ItsAlphie/The-RGB-of-Haptics/HPCT_Unity/Assets/Materials/GOLDDark.png

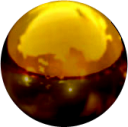
HPCT_Unity/Assets/Materials/GOLDDark.png
