ItsAlphie/The-RGB-of-Haptics/HPCT_Unity/Assets/Downloaded/jewelry_shop/textures/T_.png

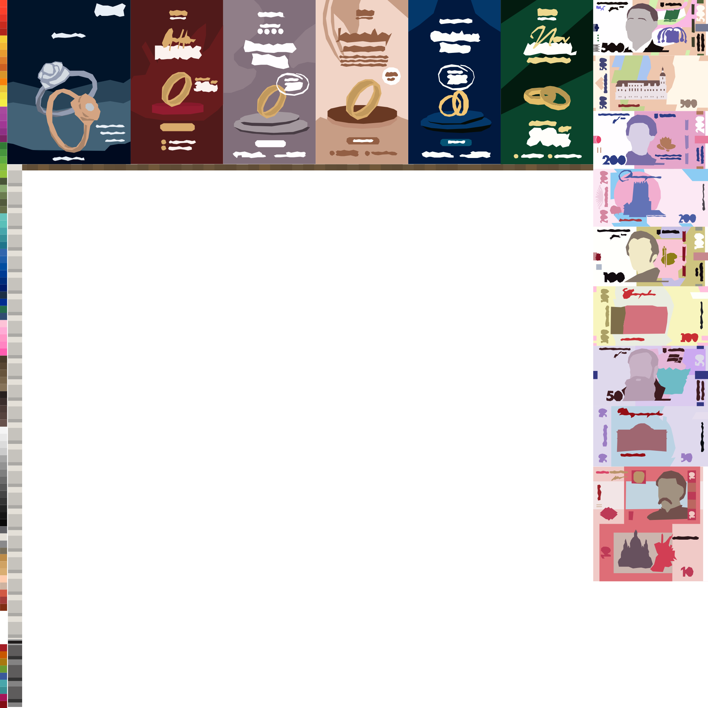
HPCT_Unity/Assets/Downloaded/jewelry_shop/textures/T_.png
