ItsAlphie/The-RGB-of-Haptics/HPCT_Unity/Assets/Mugs, Bowls and Plates/Textures/bowl01_ao.png

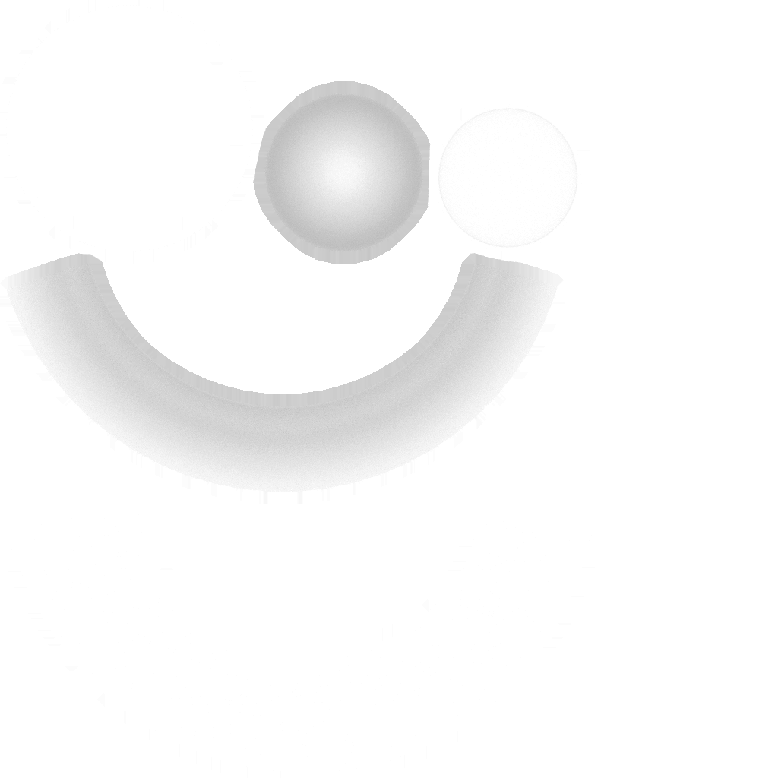
HPCT_Unity/Assets/Mugs, Bowls and Plates/Textures/bowl01_ao.png
