ItsAlphie/The-RGB-of-Haptics/HPCT_Unity/Assets/Mugs, Bowls and Plates/Textures/bowl03.png

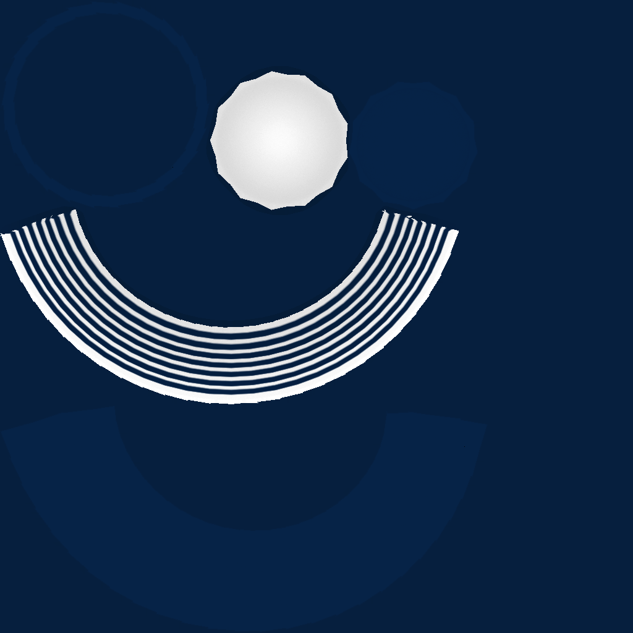
HPCT_Unity/Assets/Mugs, Bowls and Plates/Textures/bowl03.png
