ItsAlphie/The-RGB-of-Haptics/HPCT_Unity/Assets/Mugs, Bowls and Plates/Textures/mug01_rgh.png

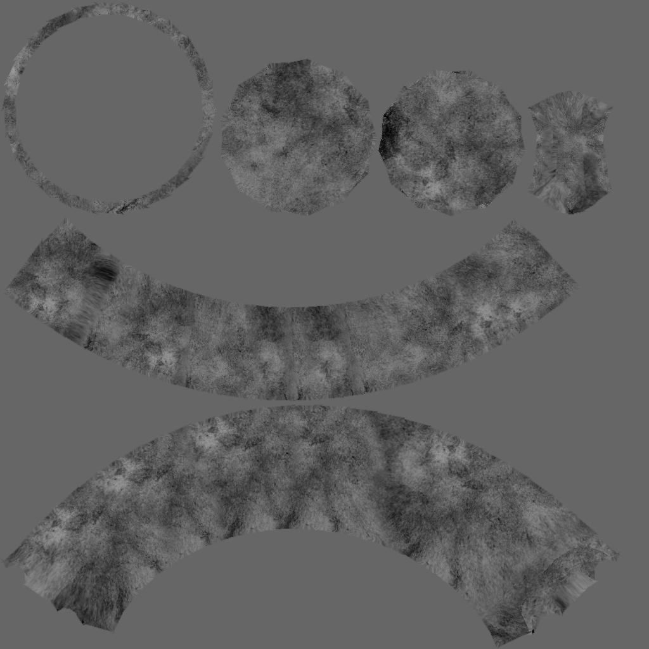
HPCT_Unity/Assets/Mugs, Bowls and Plates/Textures/mug01_rgh.png
