ItsAlphie/The-RGB-of-Haptics/HPCT_Unity/Assets/Mugs, Bowls and Plates/Textures/mug02_ao.png

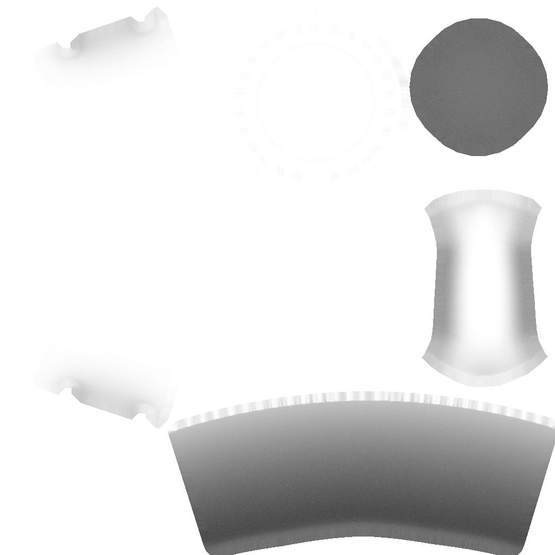
HPCT_Unity/Assets/Mugs, Bowls and Plates/Textures/mug02_ao.png
