ItsAlphie/The-RGB-of-Haptics/HPCT_Unity/Assets/Mugs, Bowls and Plates/Textures/mug02_rgh.png

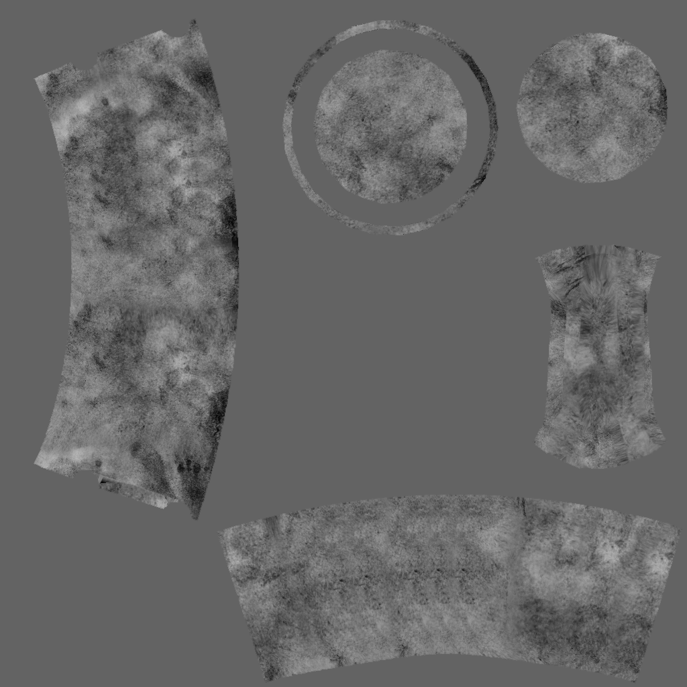
HPCT_Unity/Assets/Mugs, Bowls and Plates/Textures/mug02_rgh.png
