ItsAlphie/The-RGB-of-Haptics/HPCT_Unity/Assets/Mugs, Bowls and Plates/Textures/plate01.png

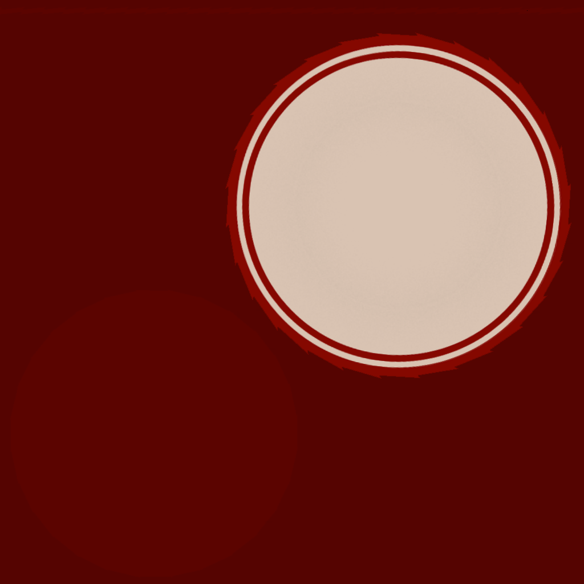
HPCT_Unity/Assets/Mugs, Bowls and Plates/Textures/plate01.png
