ItsAlphie/The-RGB-of-Haptics/HPCT_Unity/Assets/Mugs, Bowls and Plates/Textures/plate01_nm.png

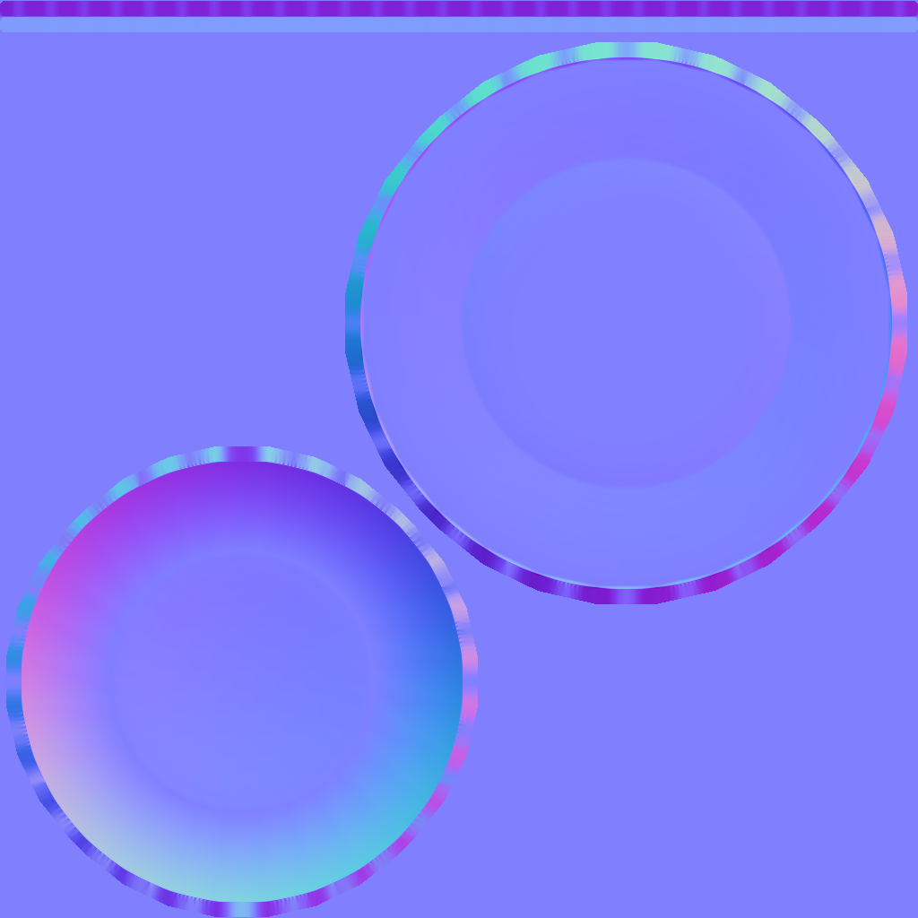
HPCT_Unity/Assets/Mugs, Bowls and Plates/Textures/plate01_nm.png
