ItsAlphie/The-RGB-of-Haptics/HPCT_Unity/Assets/Mugs, Bowls and Plates/Textures/plate01_rgh.png

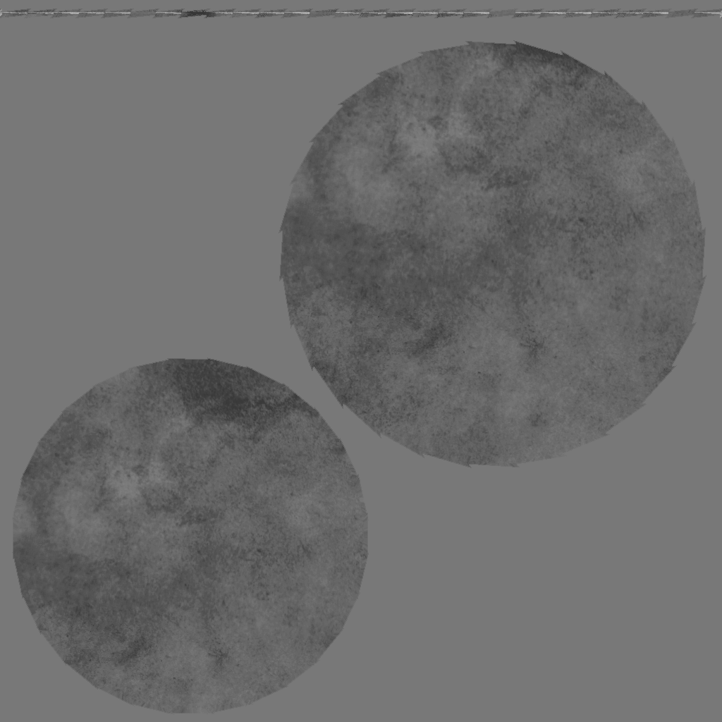
HPCT_Unity/Assets/Mugs, Bowls and Plates/Textures/plate01_rgh.png
