ItsAlphie/The-RGB-of-Haptics/HPCT_Unity/Assets/Proxy Games/Stylized Nature Kit Lite/Textures/Spruce Tree Branch.png

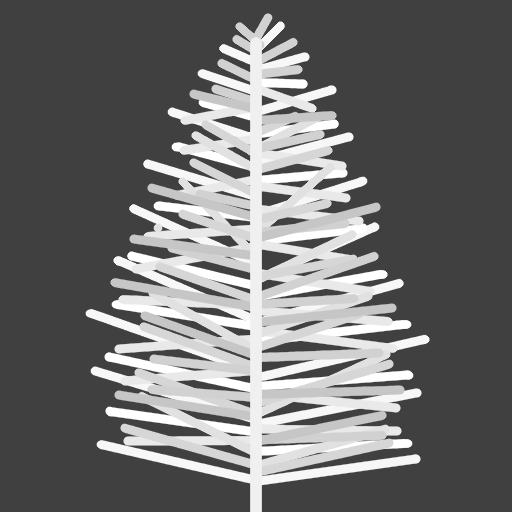
HPCT_Unity/Assets/Proxy Games/Stylized Nature Kit Lite/Textures/Spruce Tree Branch.png
