ItsAlphie/The-RGB-of-Haptics/HPCT_Unity/Assets/Samples/XR Interaction Toolkit/2.6.4/Starter Assets/DemoSceneAssets/Sprites/Round Radius 4 Outline.png

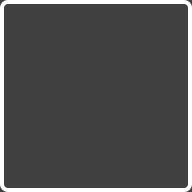
HPCT_Unity/Assets/Samples/XR Interaction Toolkit/2.6.4/Starter Assets/DemoSceneAssets/Sprites/Round Radius 4 Outline.png
