ItsAlphie/The-RGB-of-Haptics/HPCT_Unity/Assets/Scenes/BasicScene/Grid_Light_512x512.png

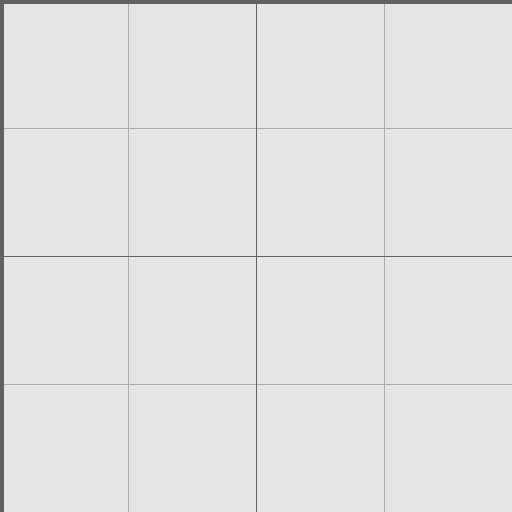
HPCT_Unity/Assets/Scenes/BasicScene/Grid_Light_512x512.png
