ItsAlphie/The-RGB-of-Haptics/HPCT_Unity/Assets/Scenes/SampleScene/Lightmap-0_comp_dir.png

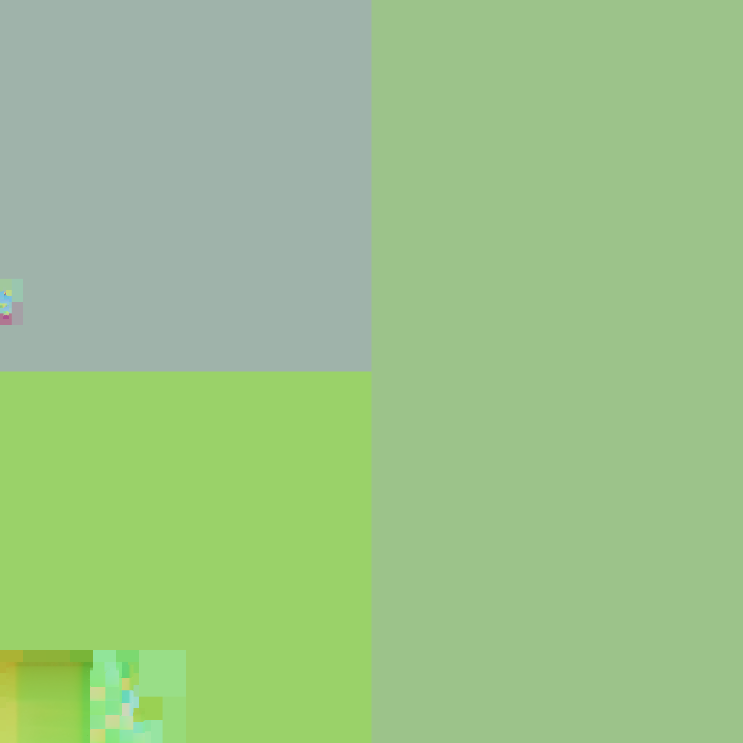
HPCT_Unity/Assets/Scenes/SampleScene/Lightmap-0_comp_dir.png
