ItsAlphie/The-RGB-of-Haptics/Paper/HPCT_Diagram.png

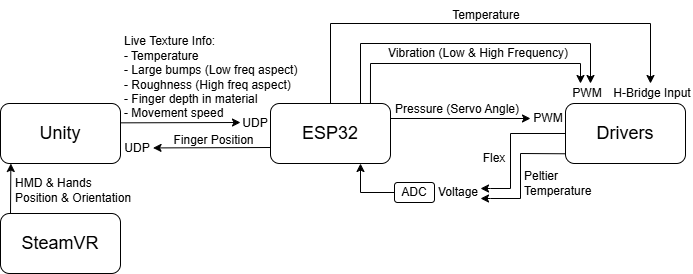
Paper/HPCT_Diagram.png
