ItsAlphie/The-RGB-of-Haptics/HPCT_Unity/Assets/Downloaded/VRTemplateAssets/Materials/Anchor Materials/Anchor Glow Gradient.png

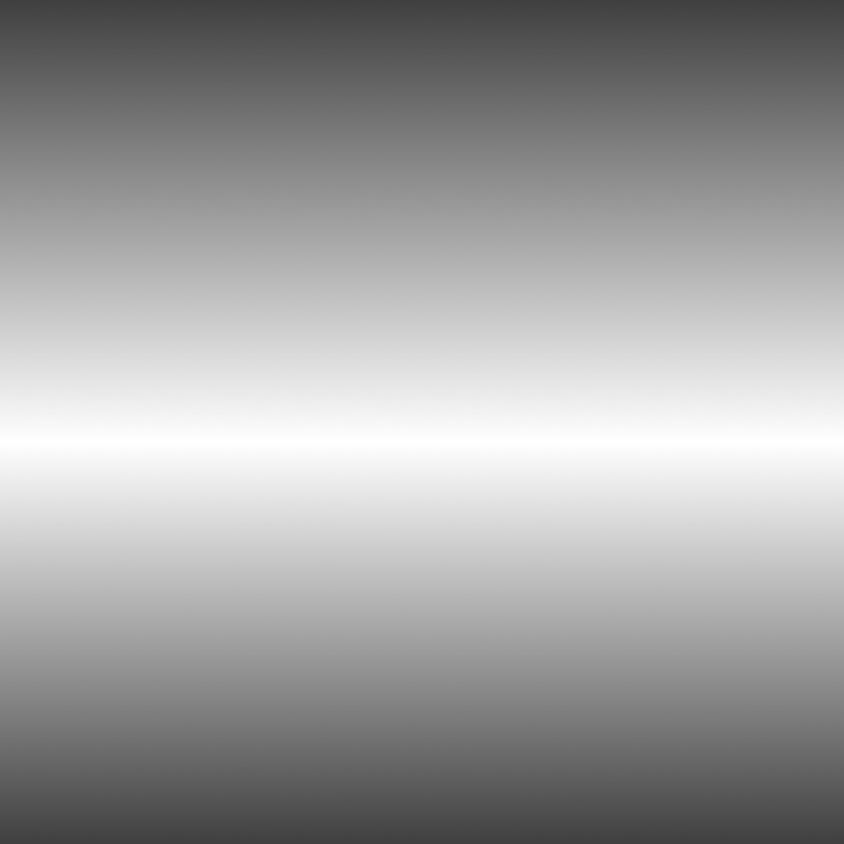
HPCT_Unity/Assets/Downloaded/VRTemplateAssets/Materials/Anchor Materials/Anchor Glow Gradient.png
