ItsAlphie/The-RGB-of-Haptics/HPCT_Unity/Assets/Downloaded/VRTemplateAssets/Materials/Anchor Materials/White_Mixed_AO.png

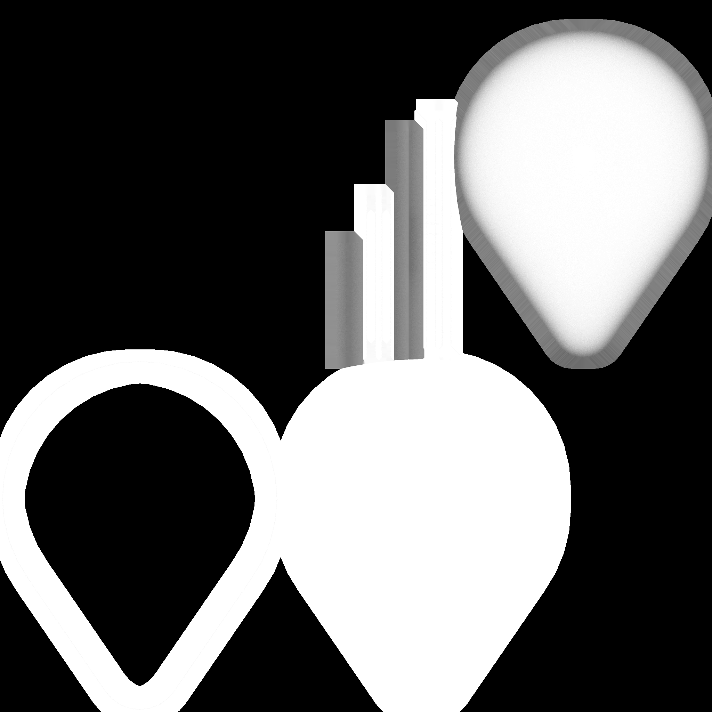
HPCT_Unity/Assets/Downloaded/VRTemplateAssets/Materials/Anchor Materials/White_Mixed_AO.png
