ItsAlphie/The-RGB-of-Haptics/HPCT_Unity/Assets/Downloaded/VRTemplateAssets/Materials/Environment/Frosted_Glass_Pattern_AlbedoTransparency.png

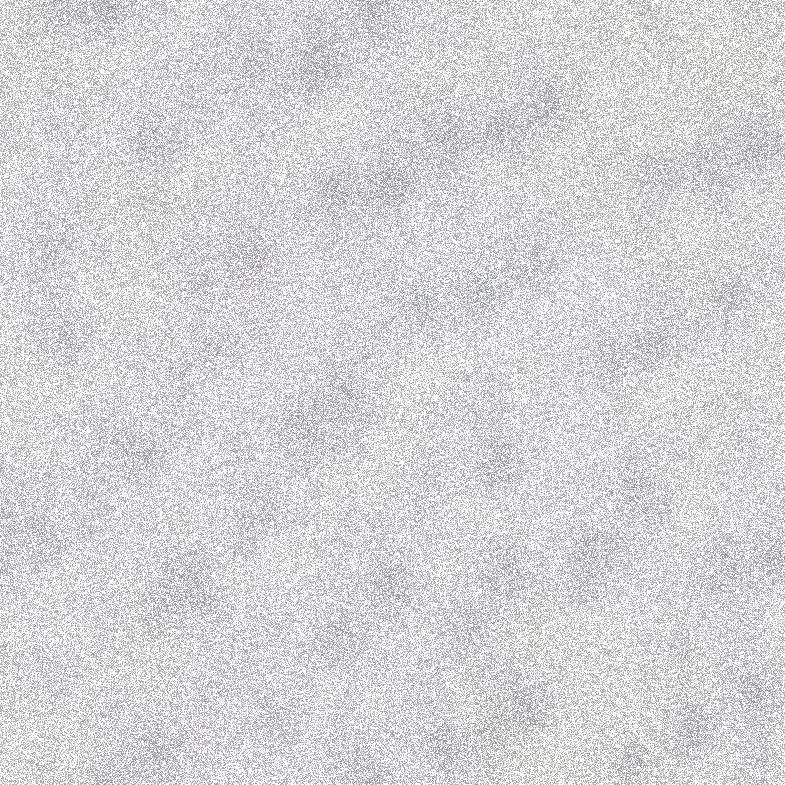
HPCT_Unity/Assets/Downloaded/VRTemplateAssets/Materials/Environment/Frosted_Glass_Pattern_AlbedoTransparency.png
