ItsAlphie/The-RGB-of-Haptics/HPCT_Unity/Assets/Downloaded/VRTemplateAssets/Materials/Environment/wall2_Roughness.png

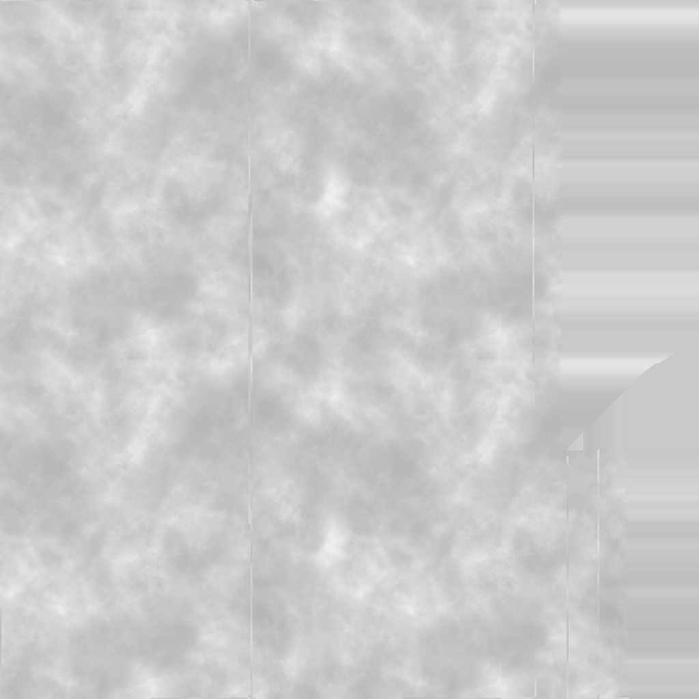
HPCT_Unity/Assets/Downloaded/VRTemplateAssets/Materials/Environment/wall2_Roughness.png
