ItsAlphie/The-RGB-of-Haptics/HPCT_Unity/Assets/Downloaded/VRTemplateAssets/Materials/Environment/wall_Normal.png

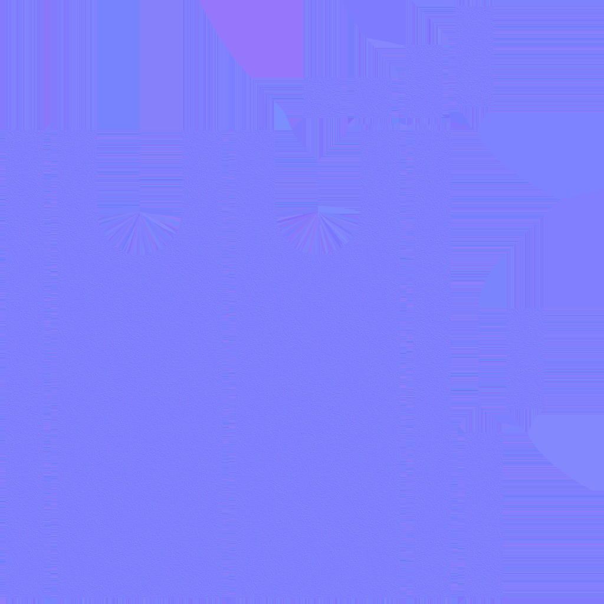
HPCT_Unity/Assets/Downloaded/VRTemplateAssets/Materials/Environment/wall_Normal.png
