ItsAlphie/The-RGB-of-Haptics/HPCT_Unity/Assets/Downloaded/VRTemplateAssets/Materials/Locomotion/BlinkOcclusionTexture.png

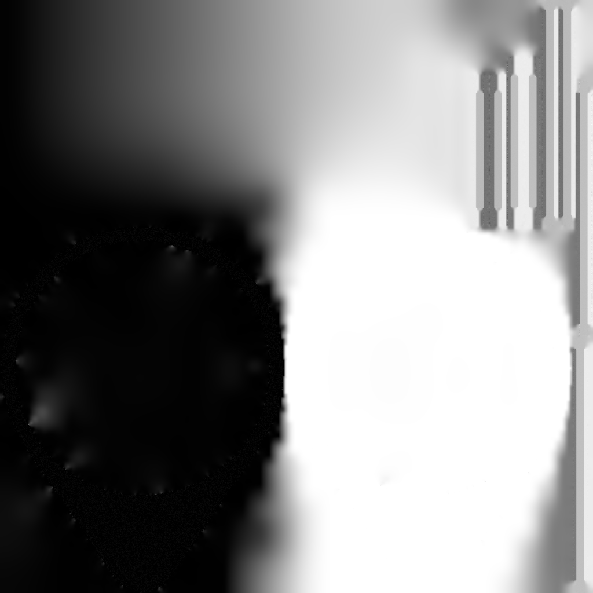
HPCT_Unity/Assets/Downloaded/VRTemplateAssets/Materials/Locomotion/BlinkOcclusionTexture.png
