ItsAlphie/The-RGB-of-Haptics/HPCT_Unity/Assets/Downloaded/VRTemplateAssets/Materials/Primitive/fabric_Height.png

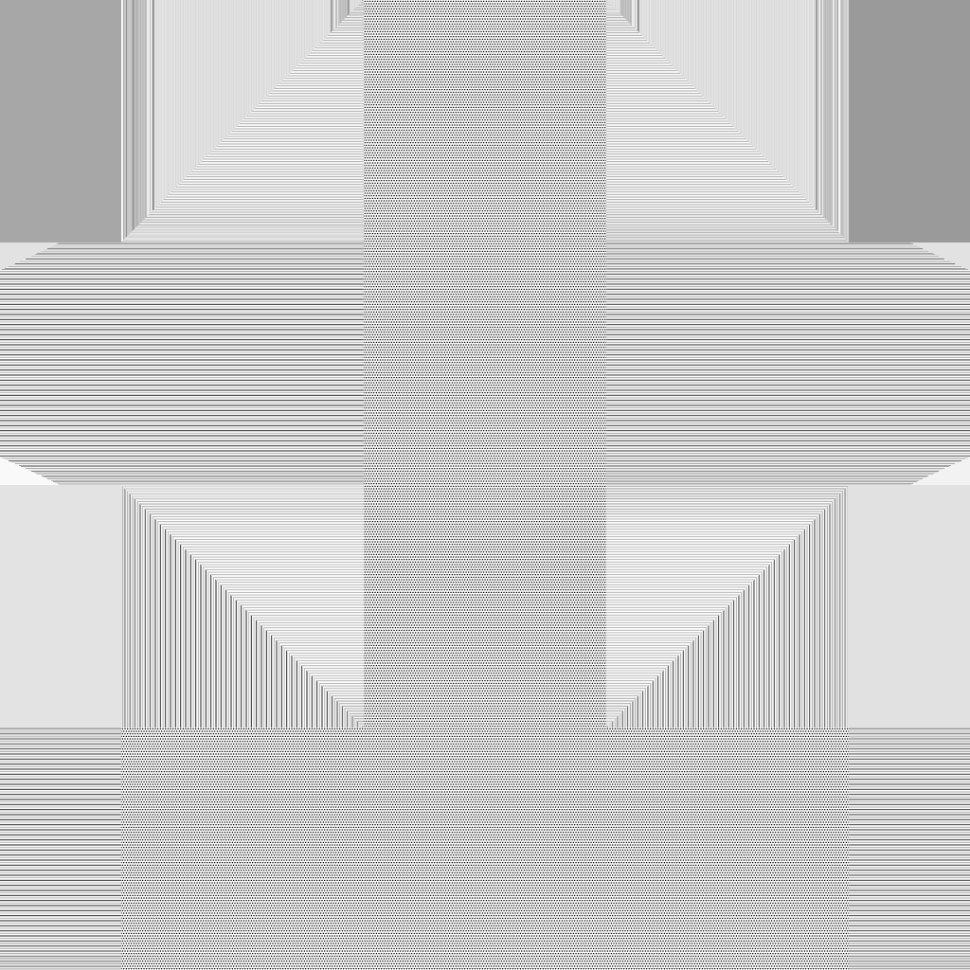
HPCT_Unity/Assets/Downloaded/VRTemplateAssets/Materials/Primitive/fabric_Height.png
