ItsAlphie/The-RGB-of-Haptics/HPCT_Unity/Assets/Downloaded/VRTemplateAssets/Materials/Primitive/fabric_Normal_OpenGL.png

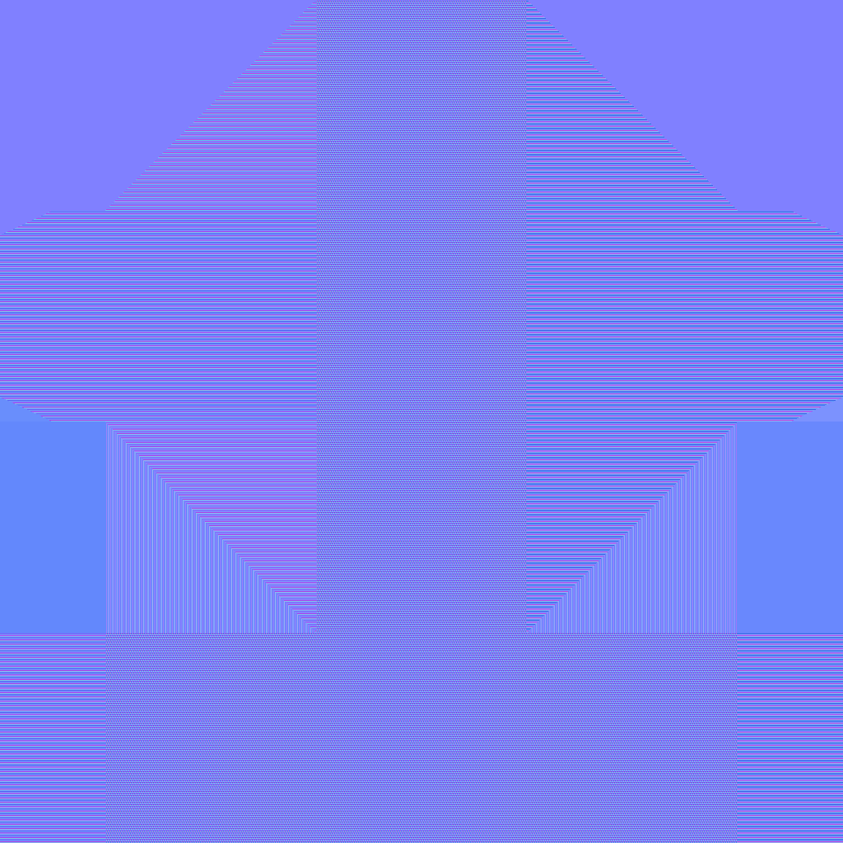
HPCT_Unity/Assets/Downloaded/VRTemplateAssets/Materials/Primitive/fabric_Normal_OpenGL.png
