ItsAlphie/The-RGB-of-Haptics/HPCT_Unity/Assets/Downloaded/VRTemplateAssets/Materials/Primitive/torus_Base_color.png

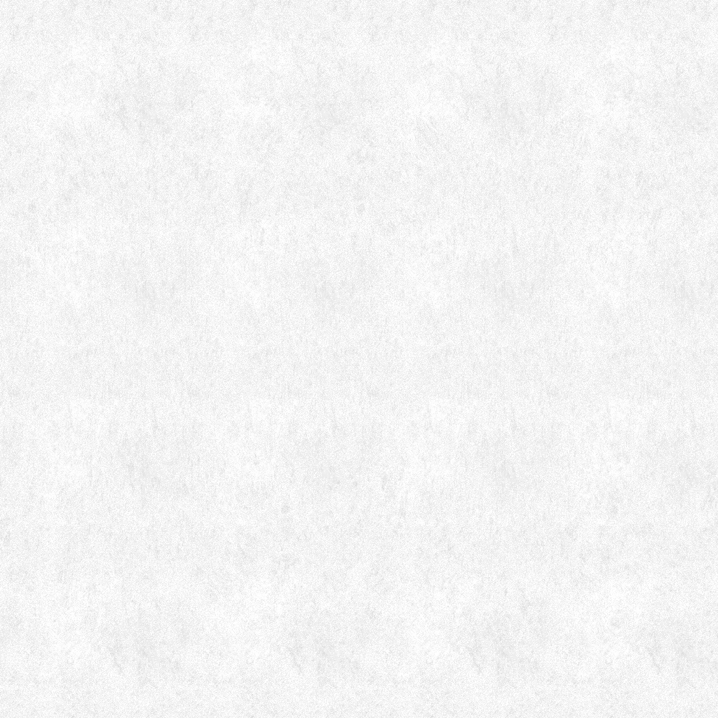
HPCT_Unity/Assets/Downloaded/VRTemplateAssets/Materials/Primitive/torus_Base_color.png
