ItsAlphie/The-RGB-of-Haptics/HPCT_Unity/Assets/Materials/19a24616f47fd975806d639b97e9e04a7e64ae3a.jpeg

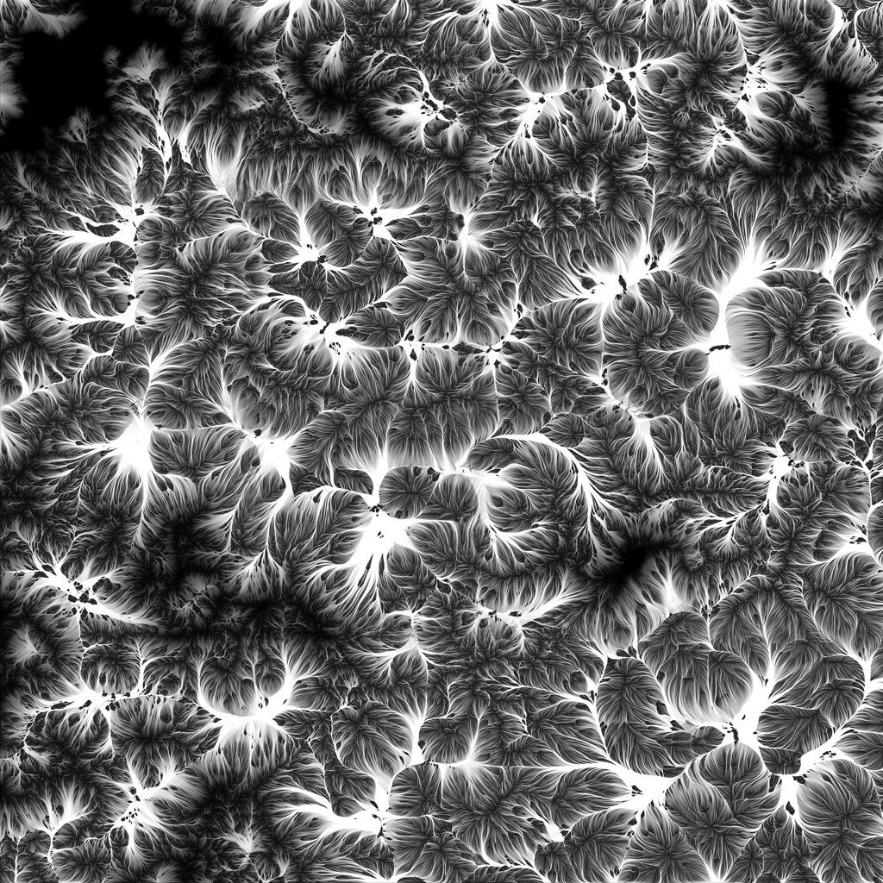
HPCT_Unity/Assets/Materials/19a24616f47fd975806d639b97e9e04a7e64ae3a.jpeg
