ItsAlphie/The-RGB-of-Haptics/HPCT_Unity/Assets/Materials/StandardShaderHeightmapTexture.jpg

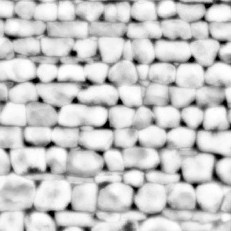
HPCT_Unity/Assets/Materials/StandardShaderHeightmapTexture.jpg
