ItsAlphie/The-RGB-of-Haptics/HPCT_Unity/Assets/Downloaded/VRTemplateAssets/Sprites/CoachingCards/Coaching Step 3.png

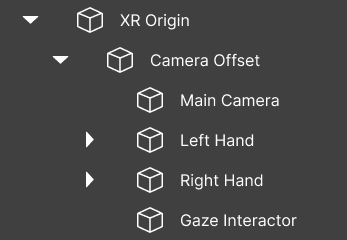
HPCT_Unity/Assets/Downloaded/VRTemplateAssets/Sprites/CoachingCards/Coaching Step 3.png
