ItsAlphie/The-RGB-of-Haptics/HPCT_Unity/Assets/Downloaded/VRTemplateAssets/Tutorial/Images/1-welcome-screen-image.png

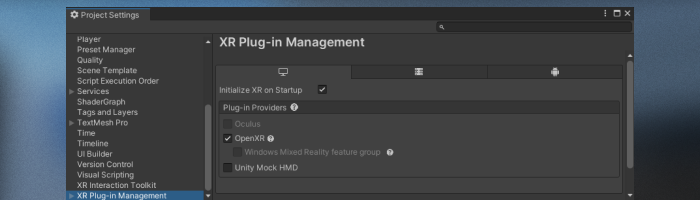
HPCT_Unity/Assets/Downloaded/VRTemplateAssets/Tutorial/Images/1-welcome-screen-image.png
