ItsAlphie/The-RGB-of-Haptics/HPCT_Unity/Assets/Downloaded/VRTemplateAssets/Tutorial/Images/project-header-vr.png

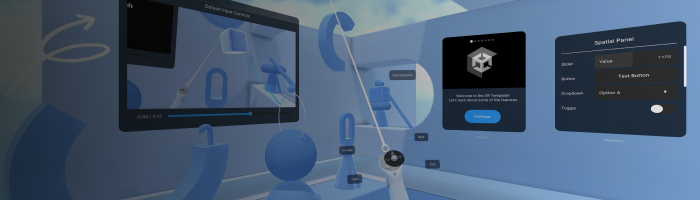
HPCT_Unity/Assets/Downloaded/VRTemplateAssets/Tutorial/Images/project-header-vr.png
